voltrabloom-source/voltrabloom-website/gallery/cad_model.png

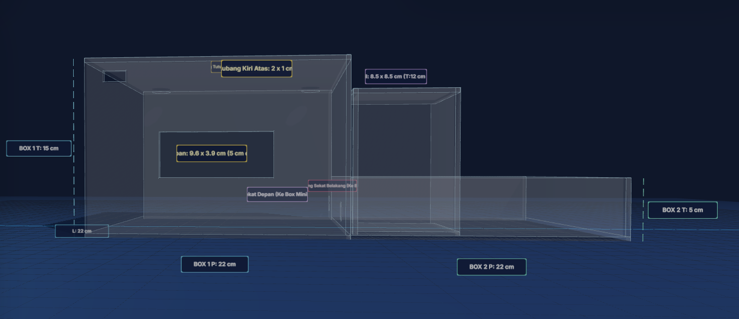
gallery/cad_model.png
