voltrabloom-source/voltrabloom-website/media/1000573353.png

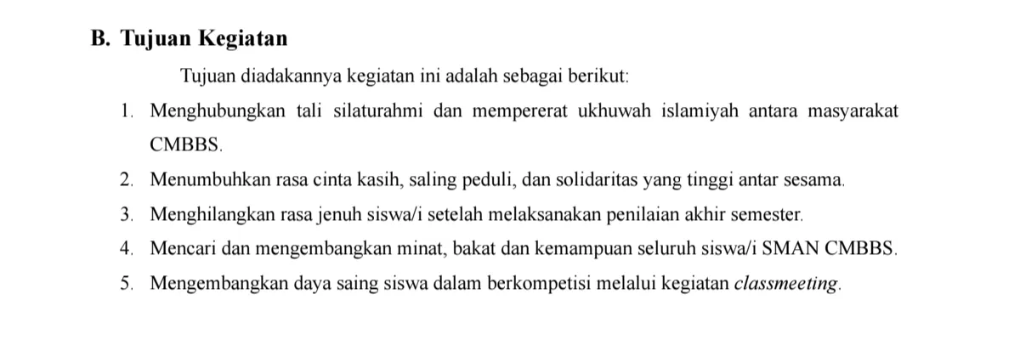
media/1000573353.png
