voltrabloom-source/voltrabloom-website/media/ChatGPT Image Aug 7, 2026, 10_49_07 AM.png

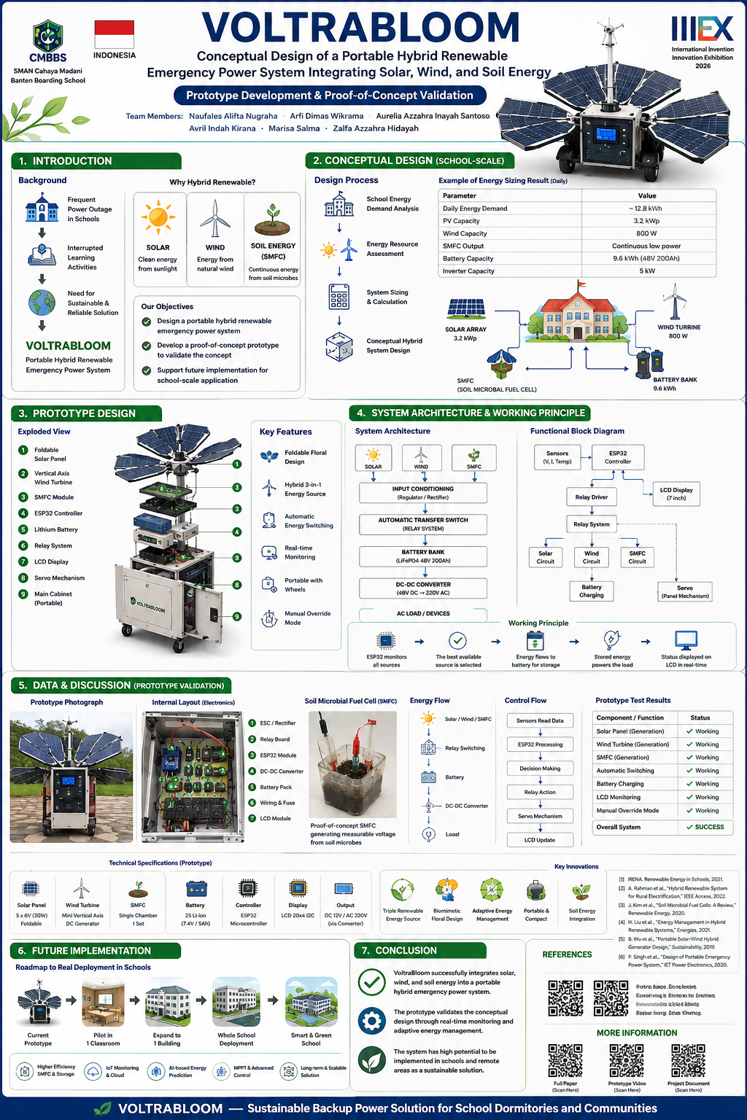
media/ChatGPT Image Aug 7, 2026, 10_49_07 AM.png
