voltrabloom-source/voltrabloom-website/media/photos/100166.jpeg

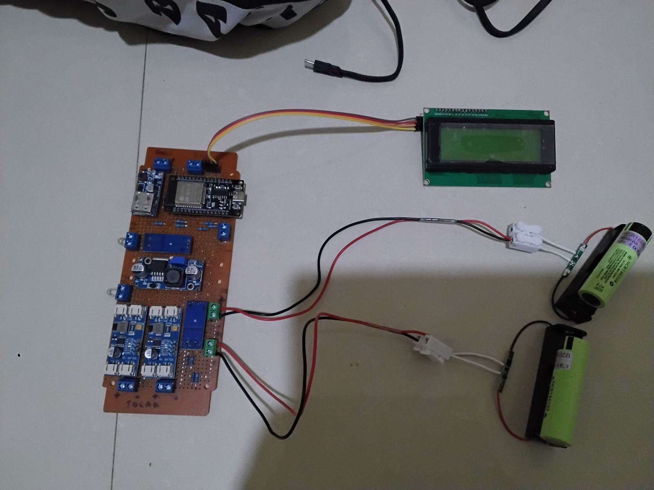
media/photos/100166.jpeg
