voltrabloom-source/voltrabloom-website/media/photos/1000115020.png

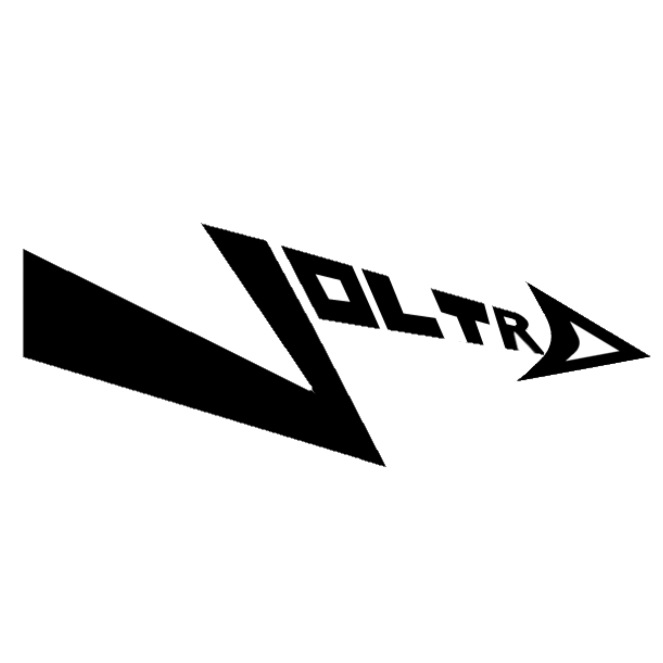
media/photos/1000115020.png
