voltrabloom-source/voltrabloom-website/media/photos/team_1.jpg

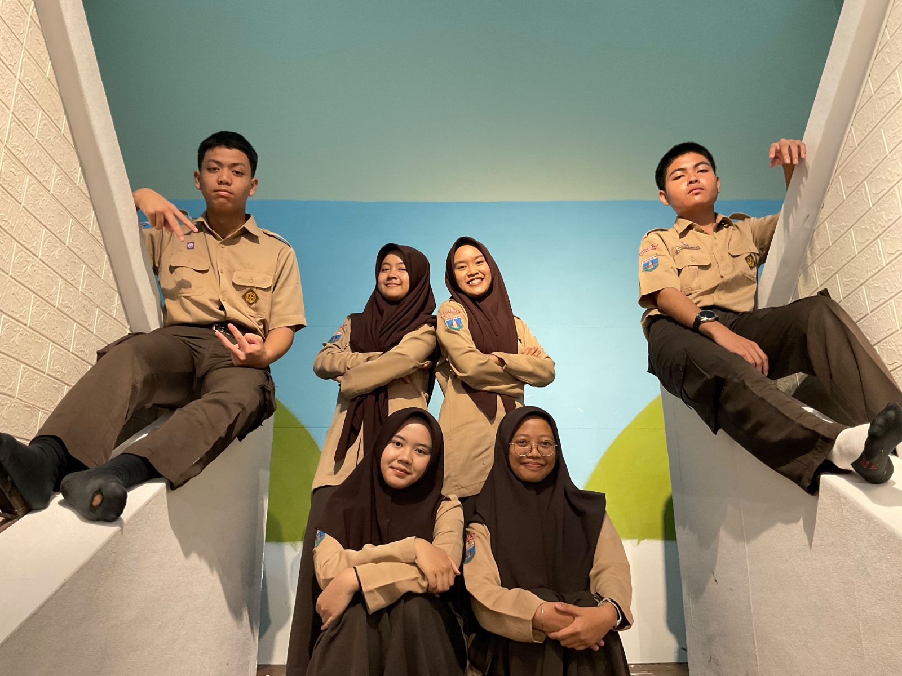
media/photos/team_1.jpg
