voltrabloom-source/voltrabloom-website/media/photos/team_2.jpg

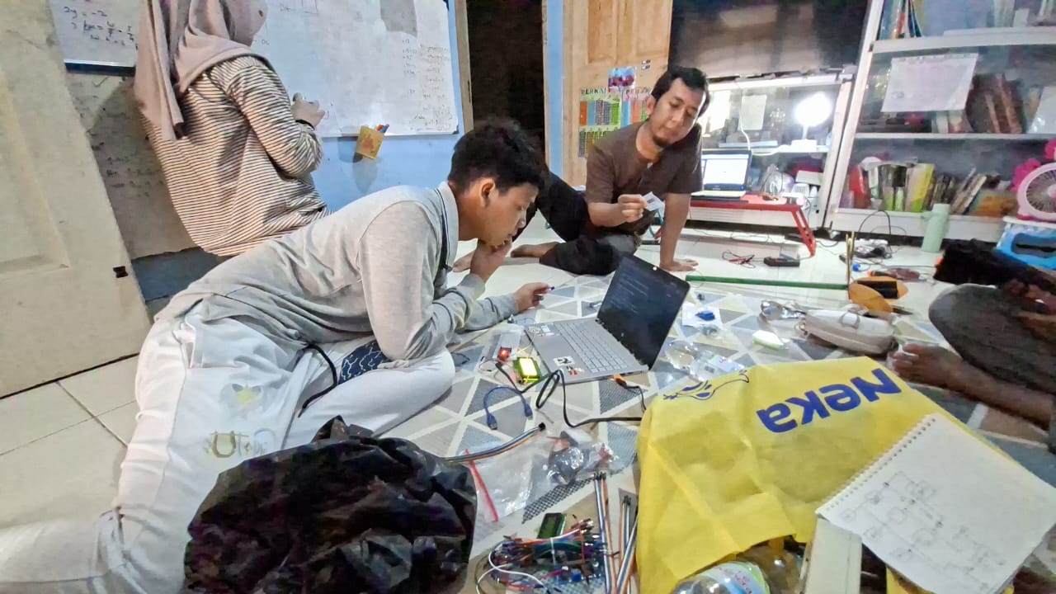
media/photos/team_2.jpg
