voltrabloom-source/voltrabloom-website/media/photos/team_3.jpg

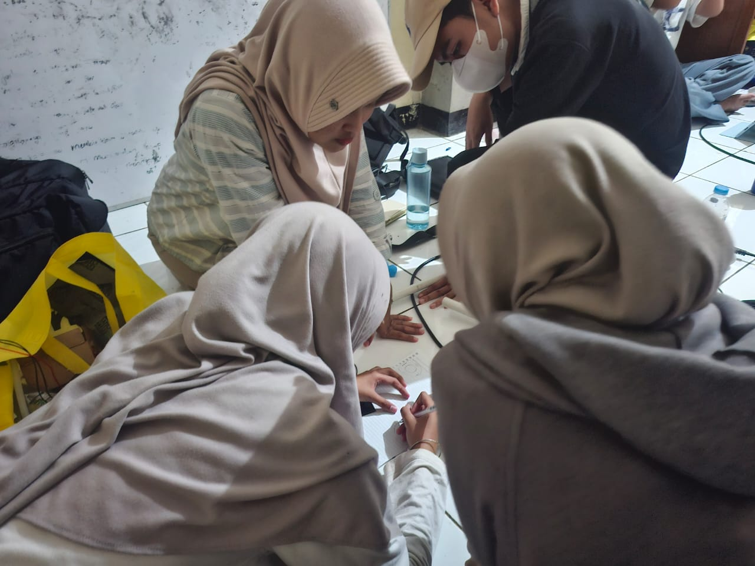
media/photos/team_3.jpg
