voltrabloom-source/voltrabloom-website/media/photos/WhatsApp_2026-08-23_07.43.30.jpeg

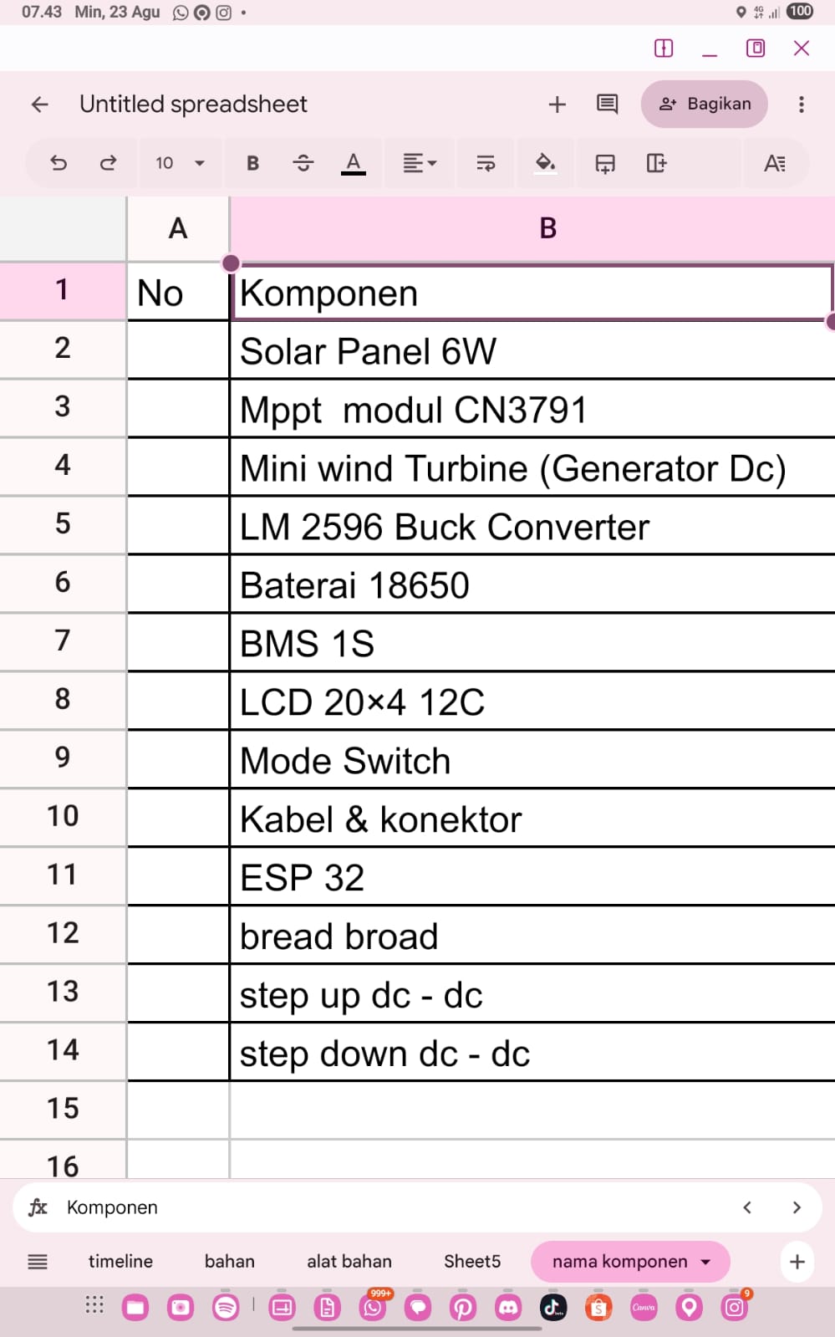
media/photos/WhatsApp_2026-08-23_07.43.30.jpeg
