voltrabloom-source/voltrabloom-website/media/screenshots/Screenshot 2026-08-23 024845.png

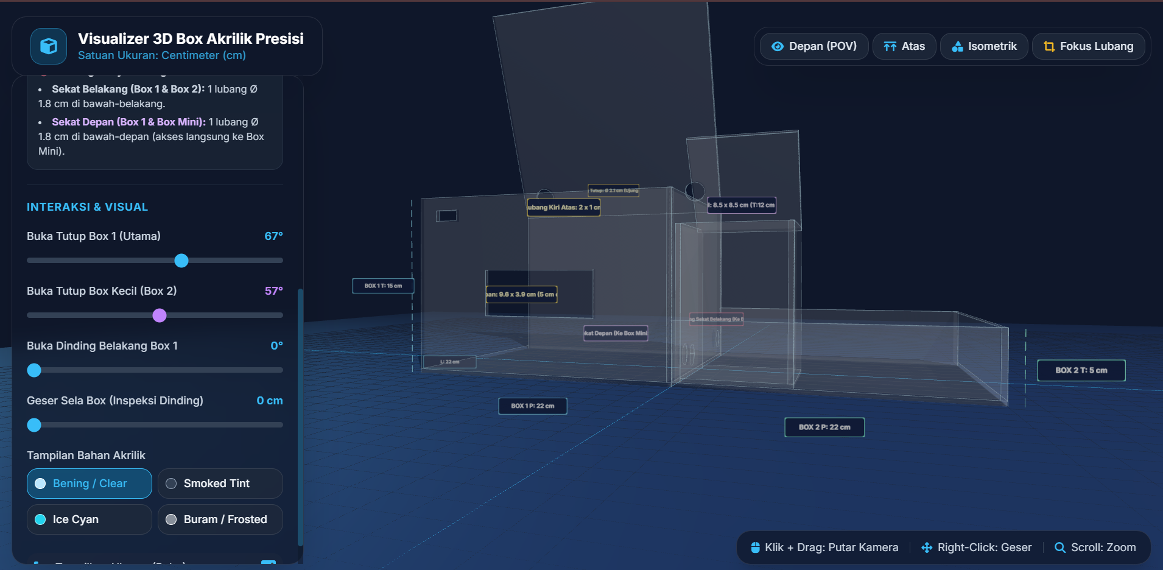
media/screenshots/Screenshot 2026-08-23 024845.png
