voltrabloom-source/voltrabloom-website/media/screenshots/Screenshot 2026-08-23 083643.png

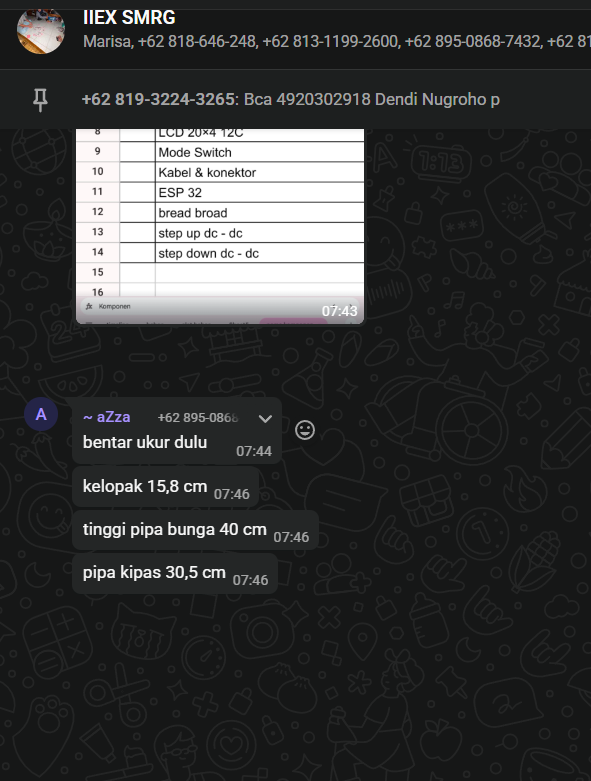
media/screenshots/Screenshot 2026-08-23 083643.png
