voltrabloom-source/voltrabloom-website/media/screenshots/Screenshot 2026-08-23 092538.png

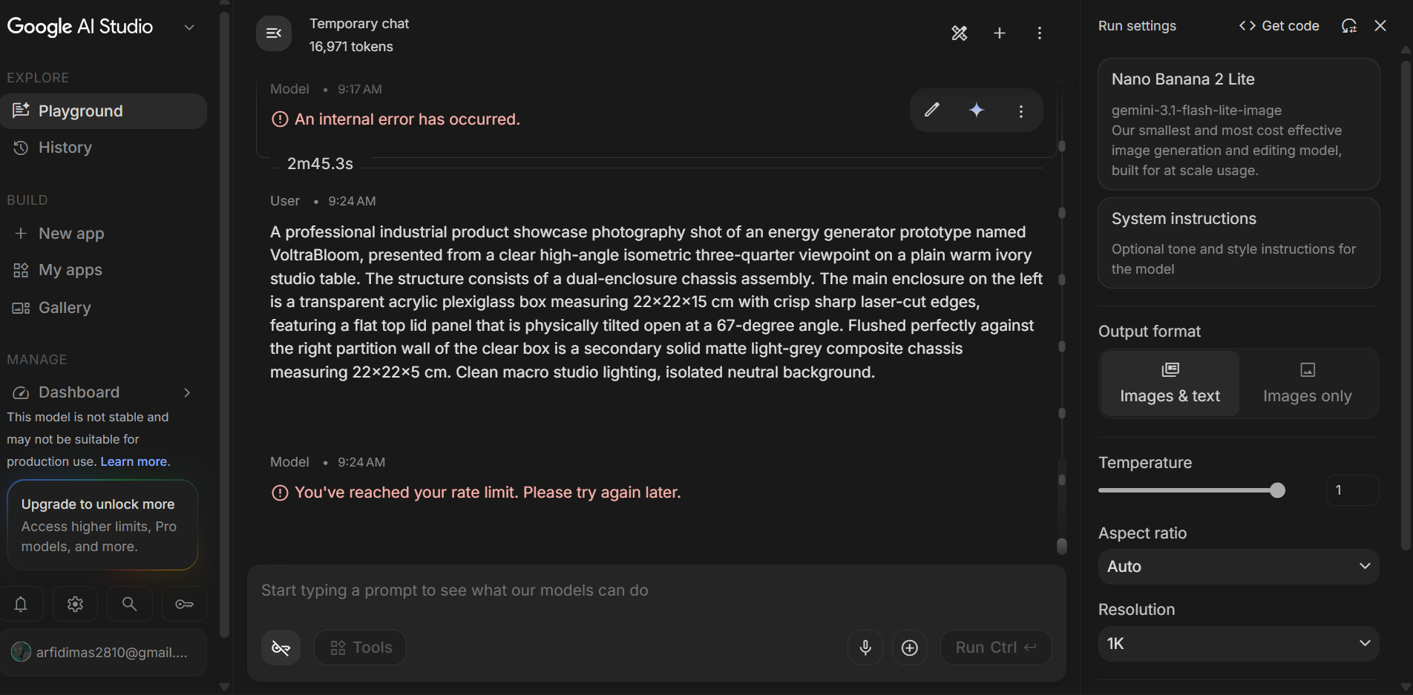
media/screenshots/Screenshot 2026-08-23 092538.png
