voltrabloom-source/voltrabloom-website/media/screenshots/Screenshot 2026-08-23 124500.png

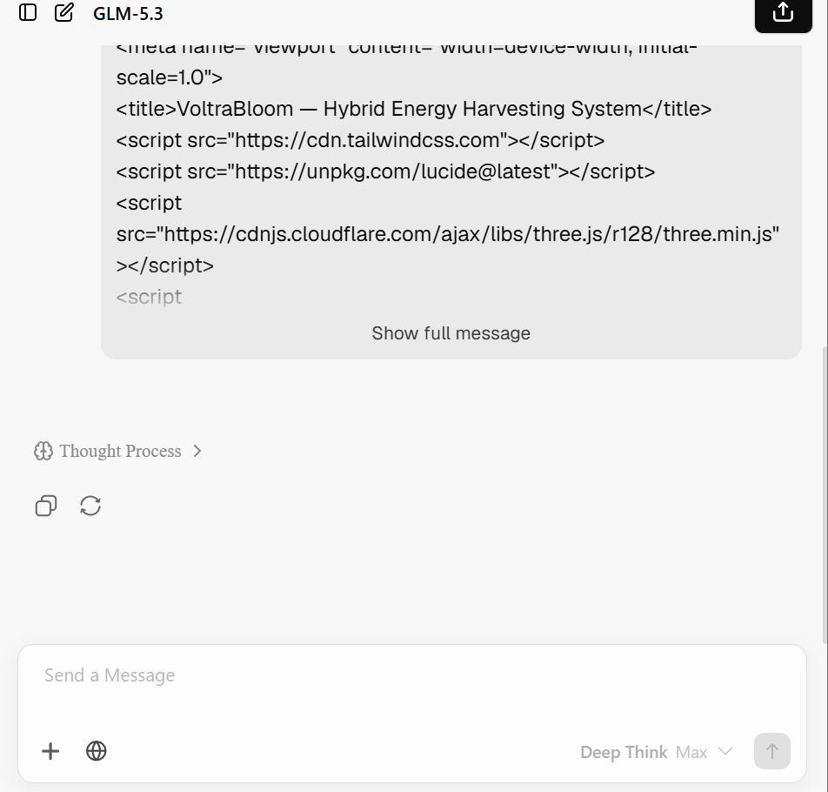
media/screenshots/Screenshot 2026-08-23 124500.png
