voltrabloom-source/voltrabloom-website/media/screenshots/Screenshot 2026-08-23 152927.png

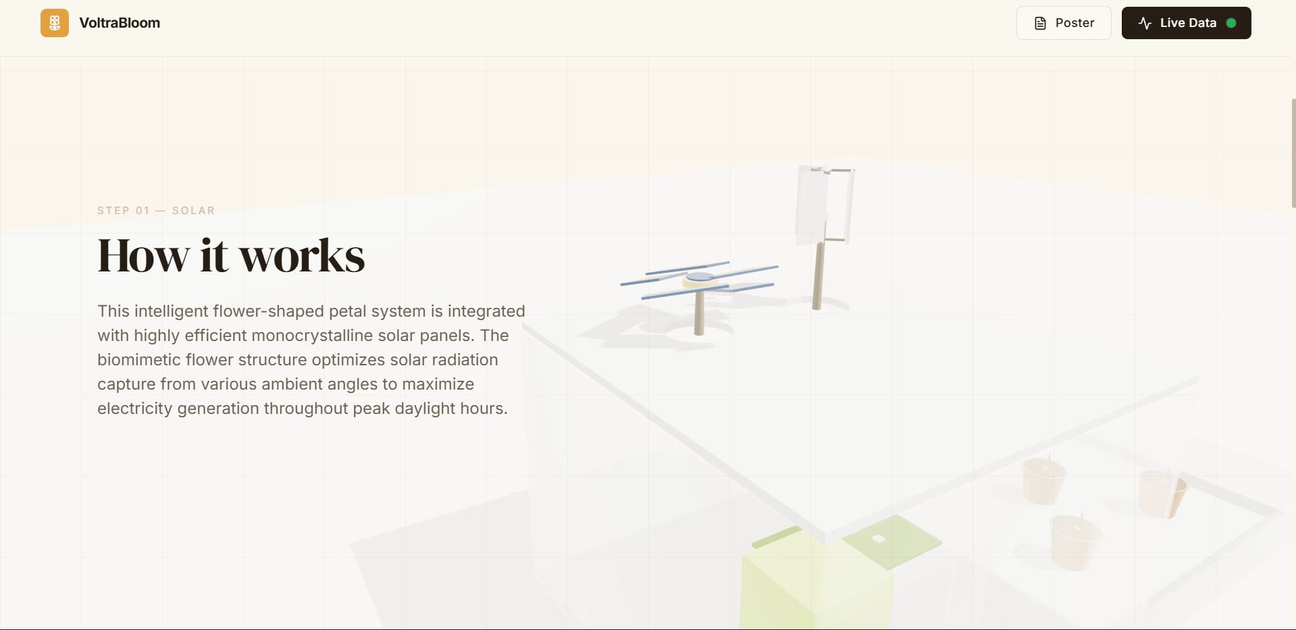
media/screenshots/Screenshot 2026-08-23 152927.png
