voltrabloom-source/voltrabloom-website/media/screenshots/Screenshot 2026-08-26 231105.png

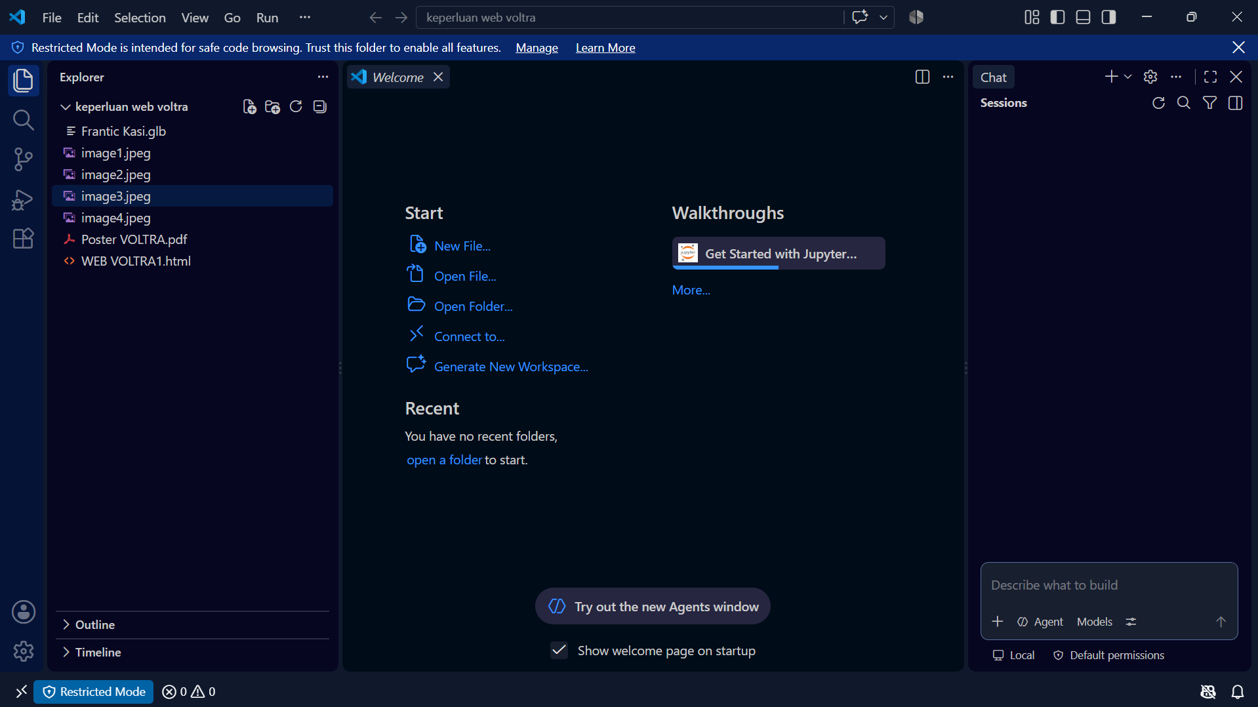
media/screenshots/Screenshot 2026-08-26 231105.png
