voltrabloom-source/voltrabloom-website/media/screenshots/Screenshot 2026-08-26 232158.png

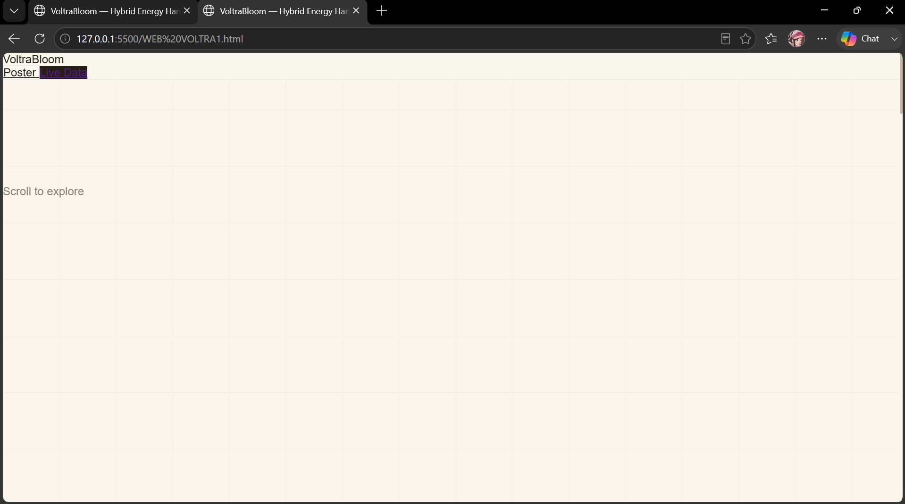
media/screenshots/Screenshot 2026-08-26 232158.png
