voltrabloom-source/voltrabloom-website/media/screenshots/Screenshot 2026-08-26 233607.png

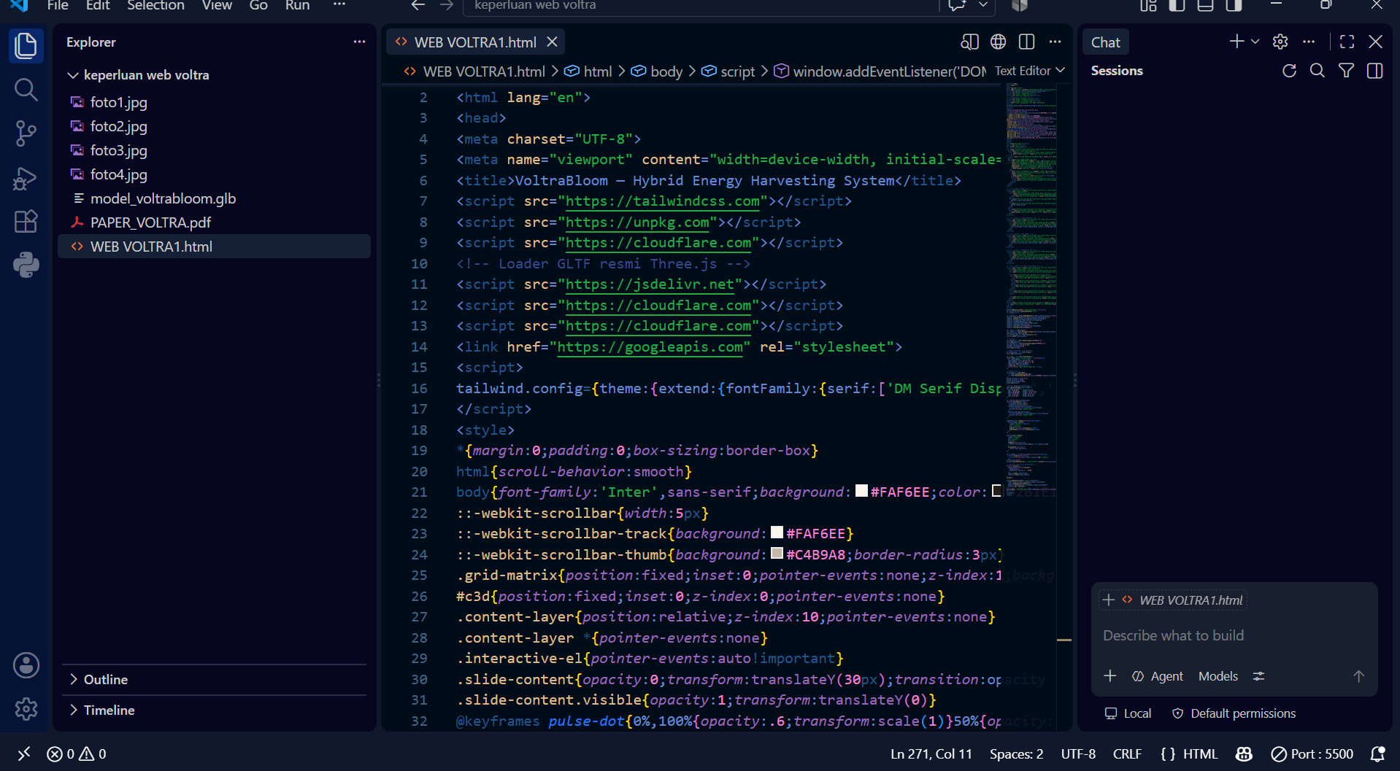
media/screenshots/Screenshot 2026-08-26 233607.png
