voltrabloom-source/voltrabloom-website/media/screenshots/Screenshot 2026-08-27 000758.png

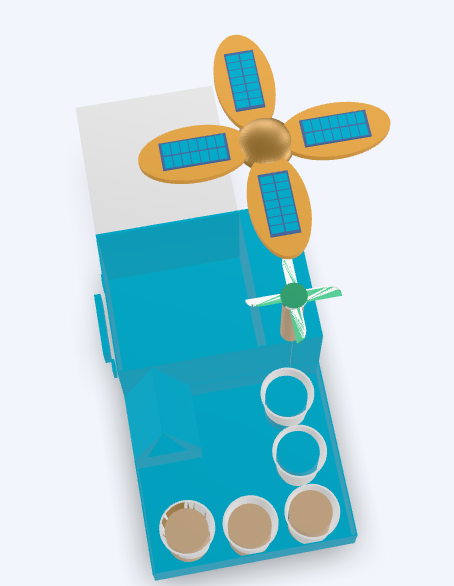
media/screenshots/Screenshot 2026-08-27 000758.png
