voltrabloom-source/voltrabloom-website/gallery/prototype_assembly.jpeg

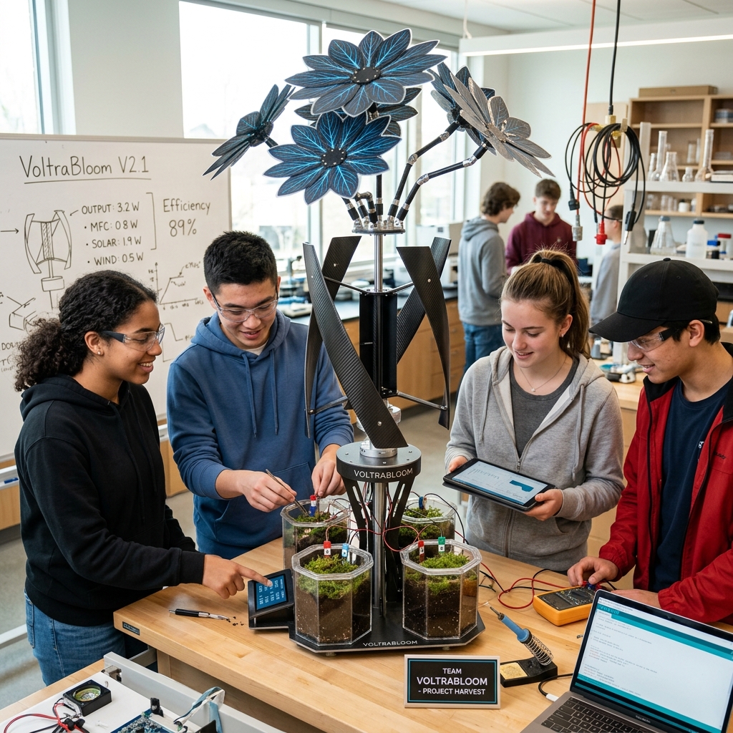
gallery/prototype_assembly.jpeg
